curiouselectric/soldersolar/SolderSolar_Instructions/Instruction_Photos/components1_sm.jpg

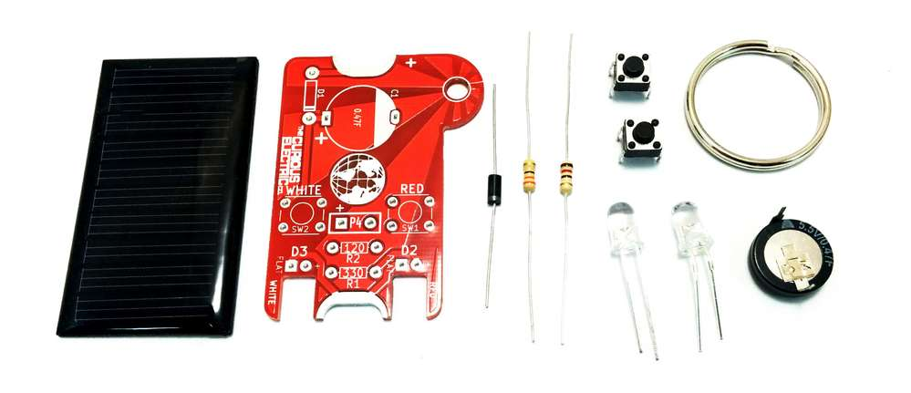
SolderSolar_Instructions/Instruction_Photos/components1_sm.jpg
