curiouselectric/soldersolar/SolderSolar_Instructions/Instruction_Photos/components2_sm_1000x750.jpg

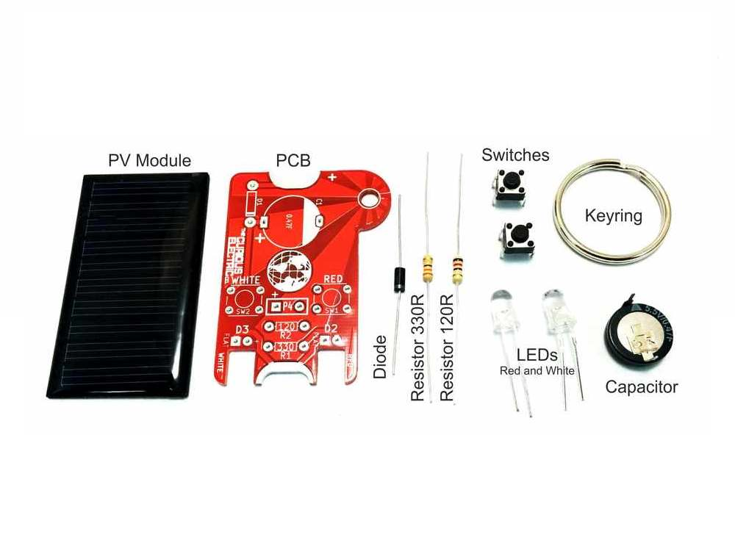
SolderSolar_Instructions/Instruction_Photos/components2_sm_1000x750.jpg
