curiouselectric/soldersolar/SolderSolar_Instructions/Instruction_Photos/InUse2_sm_1000x750.jpg

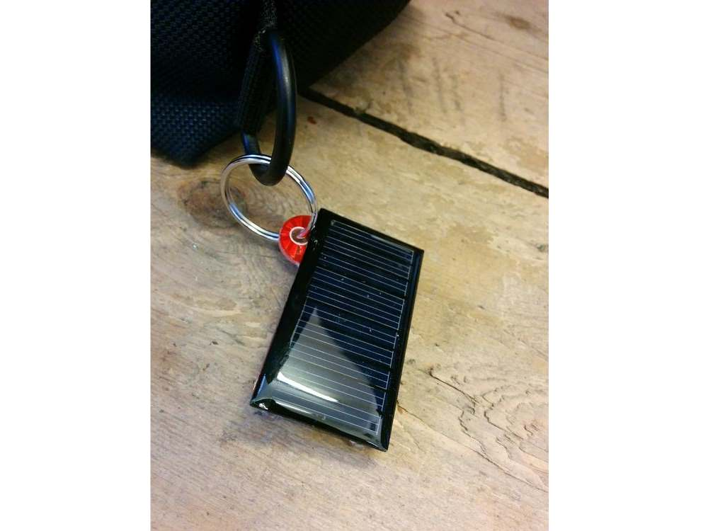
SolderSolar_Instructions/Instruction_Photos/InUse2_sm_1000x750.jpg
